heathbar/keep-talking/docs/images/game.jpg

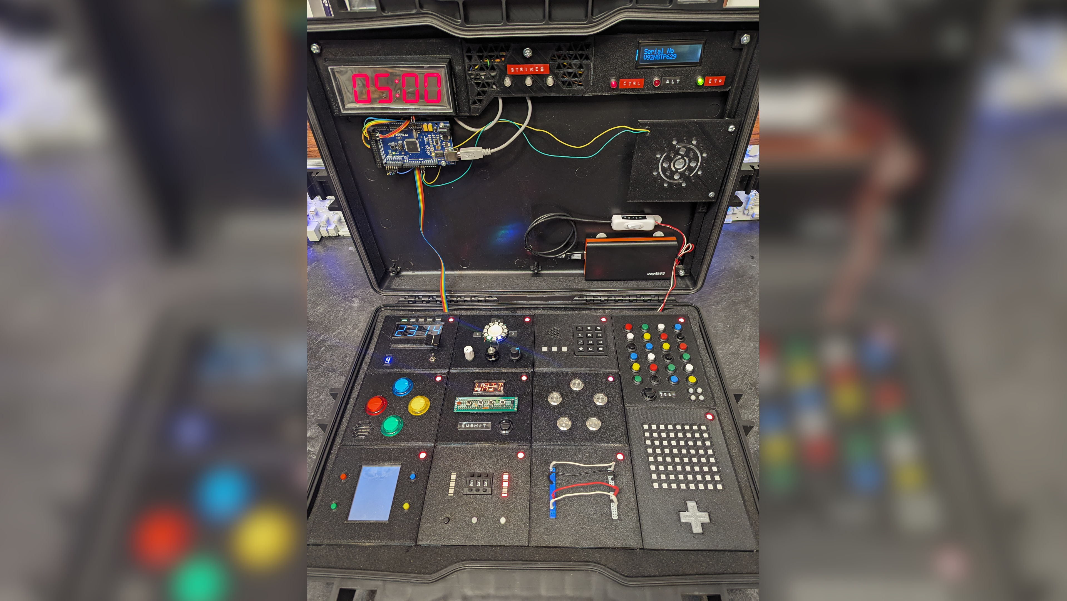
docs/images/game.jpg
