heathbar/keep-talking/docs/images/serial-loop.jpg

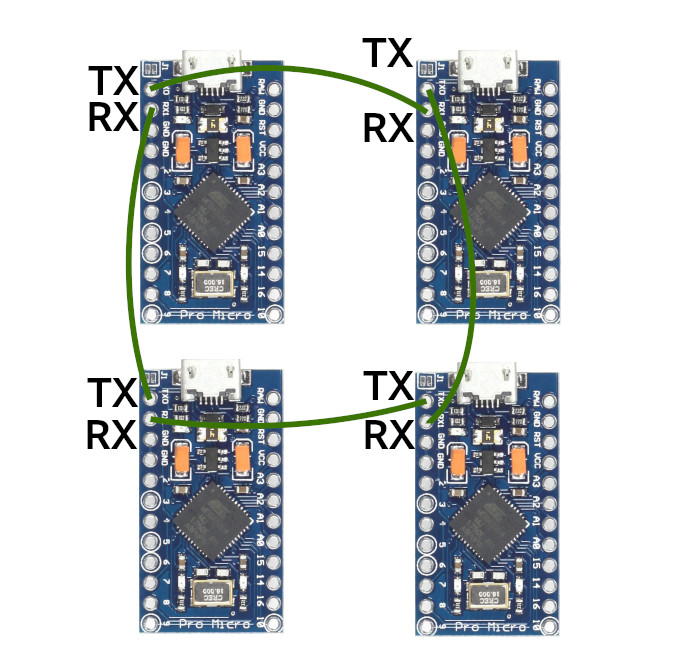
docs/images/serial-loop.jpg
