heathbar/keep-talking/module-maze/images/map1.png

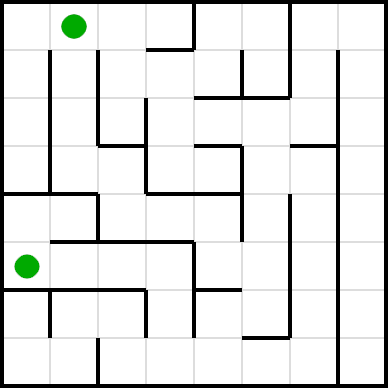
module-maze/images/map1.png
