heathbar/keep-talking/module-maze/images/map3.png

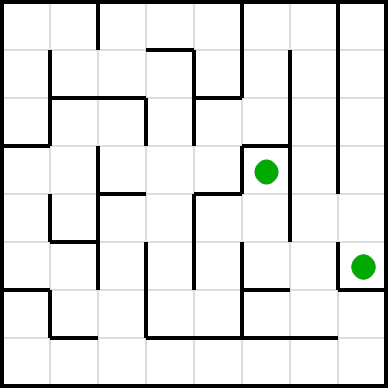
module-maze/images/map3.png
