heathbar/keep-talking/module-maze/images/map4.png

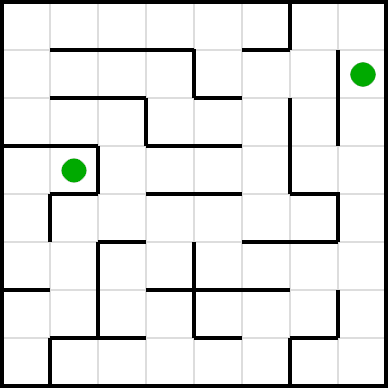
module-maze/images/map4.png
