heathbar/keep-talking/module-maze/images/map5.png

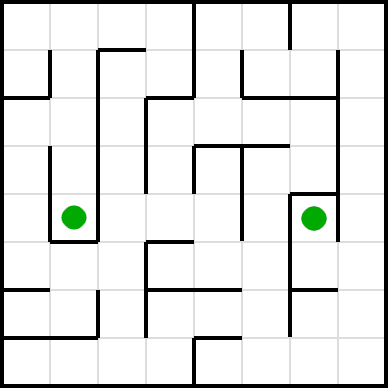
module-maze/images/map5.png
