heathbar/keep-talking/module-maze/images/map6.png

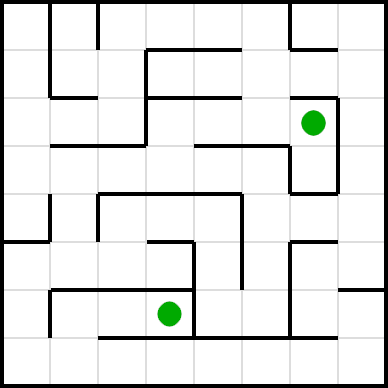
module-maze/images/map6.png
