heathbar/keep-talking/models/frame/tall midpoint horiz.stl

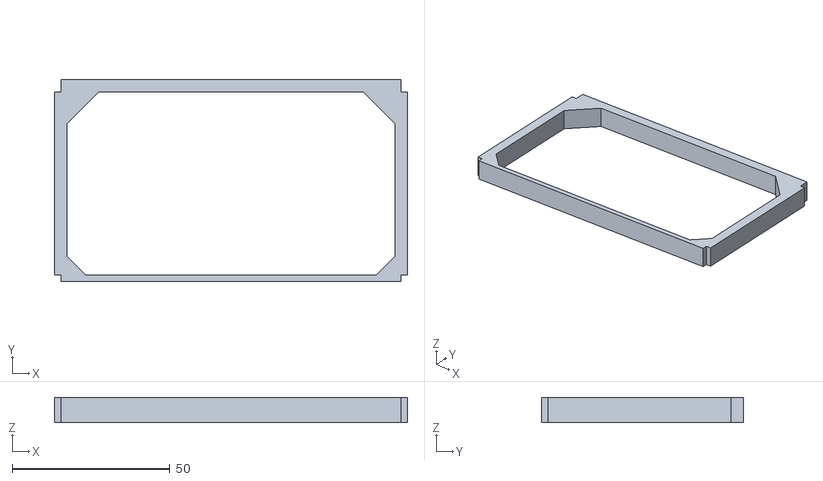
[picture p47: CAD file, 2023-04-28]
models/frame/tall midpoint horiz.stl
112.0 x 64.0 x 8.00
