heathbar/keep-talking/models/modules/dpad-block.stl

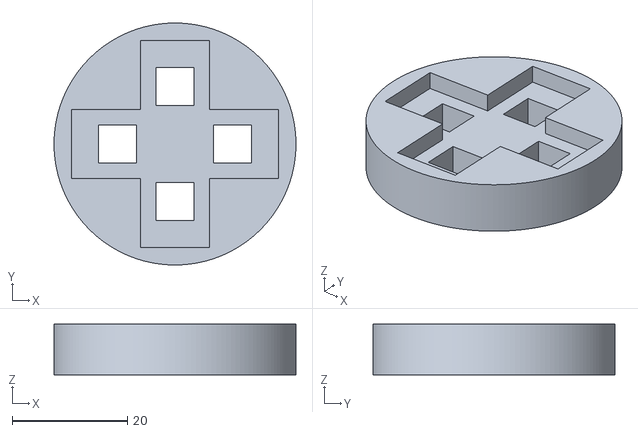
[picture p48: CAD file, 2023-04-28]
models/modules/dpad-block.stl
42.0 x 42.0 x 8.80
