heathbar/keep-talking/models/frame/Brace Vert 2.stl

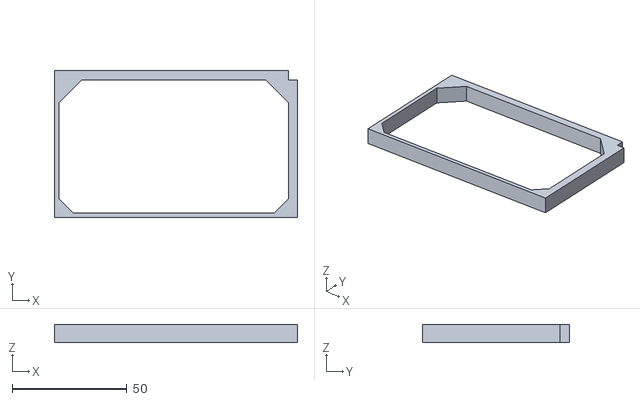
[picture p49: CAD file, 2023-04-28]
models/frame/Brace Vert 2.stl
106.0 x 64.0 x 8.00
