heathbar/keep-talking/models/modules/Maze.stl

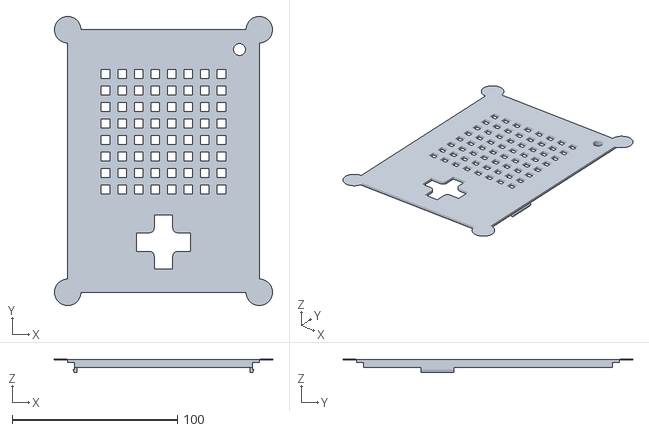
[picture p50: CAD file, 2023-04-28]
models/modules/Maze.stl
132.0 x 175.0 x 8.10
