heathbar/keep-talking/models/frame/Brace Sides.stl

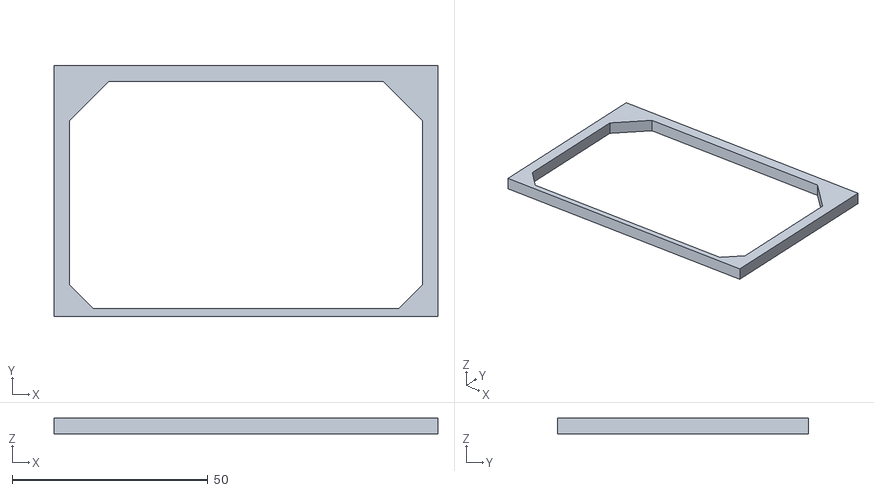
[picture p51: CAD file, 2023-04-28]
models/frame/Brace Sides.stl
98.0 x 64.0 x 4.00
