heathbar/keep-talking/models/modules/d-pad.stl

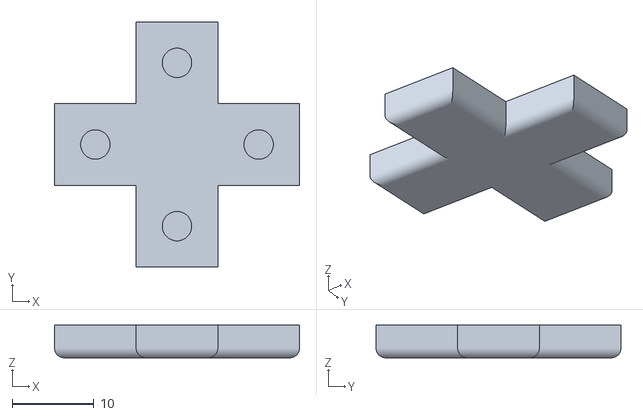
[picture p52: CAD file, 2023-04-28]
models/modules/d-pad.stl
30.0 x 30.0 x 4.00
