heathbar/keep-talking/models/frame/Brace Vert 1.stl

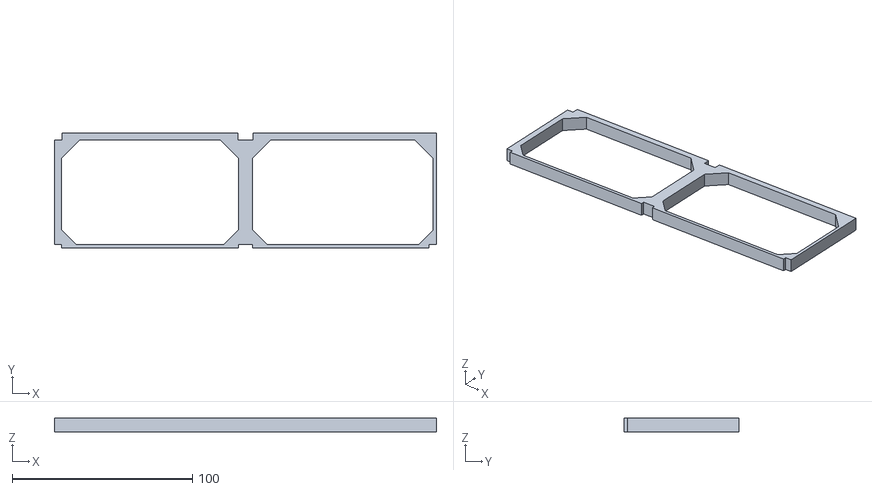
[picture p53: CAD file, 2023-04-28]
models/frame/Brace Vert 1.stl
212.0 x 64.0 x 8.00
