heathbar/keep-talking/models/modules/Mastermind.stl

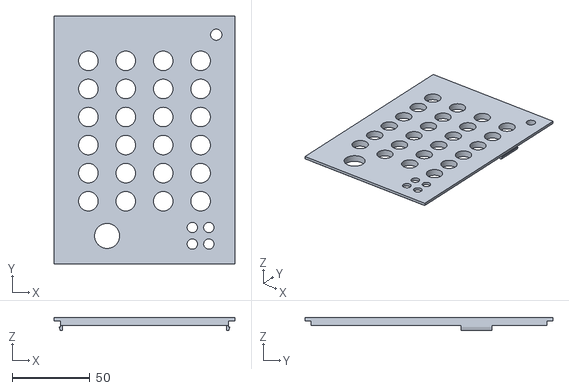
[picture p54: CAD file, 2023-04-28]
models/modules/Mastermind.stl
116.0 x 159.0 x 8.10
