heathbar/keep-talking/models/modules/Keypad-Leds.stl

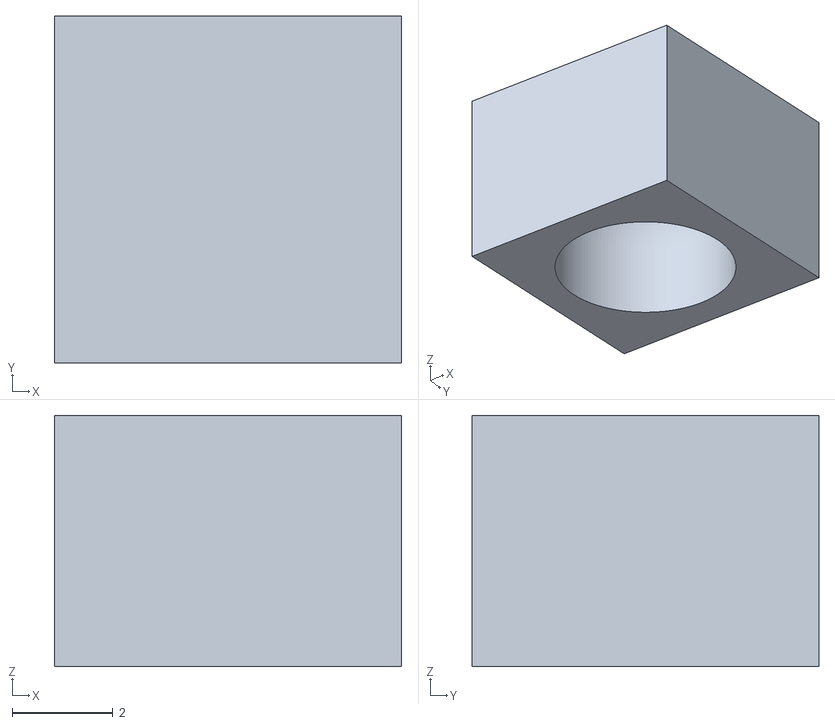
[picture p55: CAD file, 2023-04-28]
models/modules/Keypad-Leds.stl
6.90 x 6.90 x 5.00
