heathbar/keep-talking/models/modules/Keypad.stl

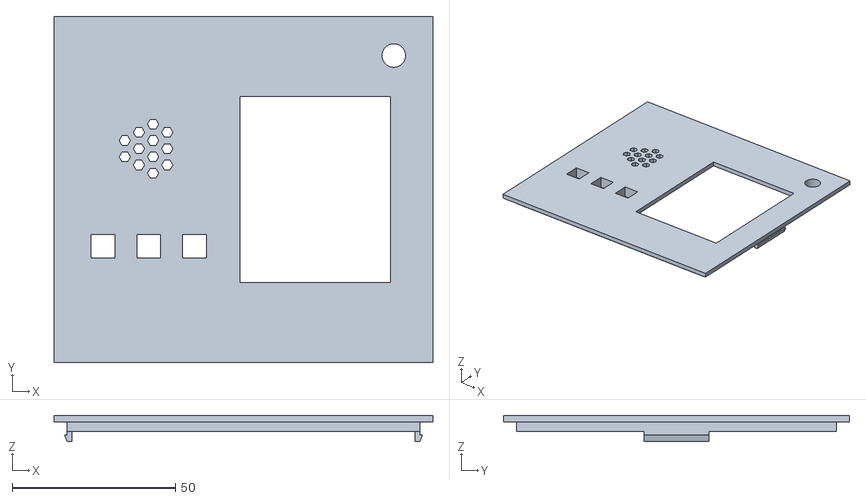
[picture p56: CAD file, 2023-04-28]
models/modules/Keypad.stl
116.0 x 106.0 x 8.10
