heathbar/keep-talking/controller/src/sounds.h

#ifndef SOUNDS_H
#define SOUNDS_H

void tone_blocking(long frequency, long length);
void tick();
void levelClear();



const char unsigned PROGMEM SND_EXPLOSION[] = {
  125, 129, 125, 130, 121, 131, 129, 122, 149, 138, 154, 163, 158, 137, 105, 87, 91, 114, 134, 149, 164, 164, 164, 168, 162, 171, 147, 139, 118, 108, 95, 83, 91, 95, 109, 142, 167, 162, 164, 164, 171, 135, 117, 97, 84, 106, 113, 116, 142, 135, 95, 92, 140, 121, 160, 178, 114, 159, 86, 124, 150, 77, 118, 30, 109, 241, 174, 214, 106, 44, 81, 81, 108, 143, 187, 166, 221, 102, 0, 8, 2, 7, 2, 9, 43, 136, 164, 164, 183, 169, 142, 172, 150, 123, 147, 145, 129, 102, 95, 66, 68, 156, 236, 254, 255, 253, 254, 252, 252, 221, 130, 96, 90, 80, 58, 39, 45, 66, 98, 128, 153, 153, 162, 129, 95, 89, 86, 81, 83, 104, 131, 140, 106, 90, 50, 35, 27, 29, 33, 68, 118, 168, 201, 154, 152, 129, 149, 174, 182, 181, 187, 205, 215, 225, 224, 228, 188, 147, 52, 4, 8, 5, 3, 5, 8, 4, 6, 0, 50, 99, 189, 245, 244, 249, 208, 152, 62, 9, 2, 4, 3, 3, 3, 3, 3, 2, 5, 2, 5, 0, 12, 41, 94, 123, 134, 166, 202, 209, 239, 245, 245, 251, 250, 251, 250, 208, 124, 128, 141, 223, 255, 249, 253, 250, 250, 250, 247, 244, 242, 228, 236, 214, 174, 40, 0, 6, 0, 6, 0, 5, 2, 14, 7, 12, 11, 40, 60, 74, 130, 186, 247, 252, 249, 253, 249, 247, 212, 178, 135, 109, 88, 68, 64, 83, 128, 137, 174, 196, 197, 190, 165, 138, 48, 14, 16, 14, 1, 12, 43, 12, 2, 6, 7, 23, 58, 56, 101, 129, 150, 206, 216, 251, 246, 251, 251, 252, 249, 252, 251, 251, 251, 251, 252, 248, 245, 193, 202, 212, 225, 218, 187, 107, 80, 52, 35, 82, 86, 65, 69, 120, 101, 167, 219, 231, 255, 246, 252, 243, 252, 253, 201, 200, 143, 110, 119, 111, 135, 131, 150, 136, 115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
8, 128, 126, 128, 126, 128, 126, 126, 128, 126, 128, 128, 128, 128, 128, 128, 126, 128, 128, 128, 128, 128, 126, 128, 128, 128, 128, 128, 126, 128, 126, 128, 128, 126, 128

};

#endif
