heathbar/keep-talking/module-hieroglyphs/src/bitmaps.h

// 'ace', 57x80px
const unsigned char epd_bitmap_ace [] PROGMEM = {
	0x03, 0xff, 0xff, 0xff, 0xff, 0xff, 0xf0, 0x00, 0x1f, 0xff, 0xff, 0xff, 0xff, 0xff, 0xfc, 0x00, 
	0x3f, 0xff, 0xff, 0xff, 0xff, 0xff, 0xfe, 0x00, 0x3f, 0xff, 0xff, 0xff, 0xff, 0xff, 0xff, 0x00, 
	0x7c, 0x00, 0x00, 0x00, 0x00, 0x00, 0x1f, 0x00, 0x78, 0x00, 0x00, 0x00, 0x00, 0x00, 0x0f, 0x00, 
	0x78, 0x00, 0x00, 0x00, 0x00, 0x00, 0x07, 0x80, 0x78, 0x00, 0x00, 0x00, 0x00, 0x00, 0x07, 0x80, 
	0x78, 0x00, 0x3e, 0x00, 0x00, 0x00, 0x07, 0x80, 0x78, 0x00, 0x7e, 0x00, 0x00, 0x00, 0x07, 0x80, 
	0x78, 0x00, 0x7e, 0x00, 0x00, 0x00, 0x07, 0x80, 0x78, 0x00, 0xff, 0x00, 0x00, 0x00, 0x07, 0x80, 
	0x78, 0x00, 0xff, 0x00, 0x00, 0x00, 0x07, 0x80, 0x78, 0x00, 0xe7, 0x00, 0x00, 0x00, 0x07, 0x80, 
	0x78, 0x01, 0xe7, 0x80, 0x00, 0x00, 0x07, 0x80, 0x78, 0x01, 0xe7, 0x80, 0x00, 0x00, 0x07, 0x80, 
	0x78, 0x01, 0xc3, 0x80, 0x00, 0x00, 0x07, 0x80, 0x78, 0x03, 0xc3, 0xc0, 0x00, 0x00, 0x07, 0x80, 
	0x78, 0x03, 0xc3, 0xc0, 0x00, 0x00, 0x07, 0x80, 0x78, 0x03, 0xc1, 0xe0, 0x00, 0x00, 0x07, 0x80, 
	0x78, 0x07, 0x81, 0xe0, 0x00, 0x00, 0x07, 0x80, 0x78, 0x07, 0x81, 0xe0, 0x00, 0x00, 0x07, 0x80, 
	0x78, 0x07, 0x00, 0xf0, 0x00, 0x00, 0x07, 0x80, 0x78, 0x0f, 0x00, 0xf0, 0x00, 0x00, 0x07, 0x80, 
	0x78, 0x0f, 0x00, 0xf0, 0x00, 0x00, 0x07, 0x80, 0x78, 0x0f, 0x00, 0xf8, 0x00, 0x00, 0x07, 0x80, 
	0x78, 0x1f, 0xff, 0xf8, 0x00, 0x00, 0x07, 0x80, 0x78, 0x1f, 0xff, 0xf8, 0x00, 0x00, 0x07, 0x80, 
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
	0x7e, 0x00, 0x1f, 0xc0, 0x00, 0x00, 0x1f, 0x80, 0x00, 0x00, 0x7f, 0x00, 0x1f, 0x80, 0x00, 0x00, 
	0x1f, 0x80, 0x00, 0x00, 0x3f, 0x80, 0x3f, 0x80, 0x00, 0x00, 0x1f, 0x80, 0x00, 0x00, 0x1f, 0x80, 
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
};
