heathbar/keep-talking/module-hieroglyphs/src/rando.h

#include <Arduino.h>

const int waitTime = 16;

byte lastByte = 0;

byte leftStack = 0;
byte rightStack = 0;

byte rotate(byte b, int r) {
  return (b << r) | (b >> (8-r));
}

void pushLeftStack(byte bitToPush) {
  leftStack = (leftStack << 1) ^ bitToPush ^ leftStack;
}
void pushRightStackRight(byte bitToPush) {
  rightStack = (rightStack >> 1) ^ (bitToPush << 7) ^ rightStack;
}



byte getTrueRotateRandomByte() {
  byte finalByte = 0;
  
  byte lastStack = leftStack ^ rightStack;
  
  for (int i=0; i<4; i++) {
    delayMicroseconds(waitTime);
    int leftBits = analogRead(A5);
    
    delayMicroseconds(waitTime);
    int rightBits = analogRead(A5);
    
    finalByte ^= rotate(leftBits, i);
    finalByte ^= rotate(rightBits, 7-i);
    
    for (int j=0; j<8; j++) {
      byte leftBit = (leftBits >> j) & 1;
      byte rightBit = (rightBits >> j) & 1;
  
      if (leftBit != rightBit) {
        if (lastStack % 2 == 0) {
          pushLeftStack(leftBit);
        } else {
          pushRightStackRight(leftBit);
        }
      }
    }
    
  }
  lastByte ^= (lastByte >> 3) ^ (lastByte << 5) ^ (lastByte >> 4);
  lastByte ^= finalByte;
  
  return lastByte ^ leftStack ^ rightStack;
}

int random6() {
  return getTrueRotateRandomByte() % 6;
}
