heathbar/keep-talking/module-simon-says/src/MusicNotes.h

#ifndef MusicNotes_h
#define MusicNotes_h

const inline short piezoPin = 13;

inline unsigned int NOTE_F4 = 349;
inline unsigned int NOTE_E4 = 330;
inline unsigned int NOTE_D4 = 294;
inline unsigned int NOTE_C4 = 262;

#endif
